IESAljada/RedMeteo/Software/secrets.h

// Use this file to store all of the private credentials 
// and connection details

// Enter a MAC address for your controller below.
// Newer Ethernet shields have a MAC address printed on a sticker on the shield
//#define SECRET_MAC {0x90, 0xA2, 0xDA, 0x10, 0x40, 0x4F}
#define SECRET_MAC {0xDE, 0xAD, 0xBE, 0xEF, 0xFE, 0xED}

#define SECRET_CH_ID *******			// replace 0000000 with your channel number
#define SECRET_WRITE_APIKEY "***************"   // replace XYZ with your channel write API Key
